thjaed/PicoCharts/src/state.py

class WiFi:
    connected = False
class UI:
    sleeping = False
    last_interaction_time = 0
    reset_page_after_sleep = False
class LED:
    status = []
class Homework:
    unseen_ids = []
class Battery:
    connected = False
class Clock:
    rtc_set = False
