thjaed/PicoCharts/src/secrets.py

# Your ClassCharts pupil code used to login to the app and website
CC_CODE = "Pupil Code"
# Your date of birth in the form YYYY-MM-DD
CC_DOB = "YYYY-MM-DD"

# Saved WiFi Networks
WIFI_NETWORKS = {
    "SSID": "PASSWORD",
    "Another SSID": "Another PASSWORD"
}

# Examples:
'''
WIFI_NETWORKS = {
    "Home WiFi": "123456abcd",
    "School WiFi": "defg4567",
    "Phone Hotspot": "zxcvbnm986"
}

WIFI_NETWORKS = {
    "Home WiFi": "123456abcd"
}
'''
